goldeneas/potxii/src/led_pwm.py

from machine import Pin, PWM

class LedPWM:
    def __init__(self, pin_id, max_pwm_value=1023):
        self._pin = Pin(pin_id, Pin.OUT)
        self._max_pwm_value = max_pwm_value
        self._pwm = PWM(self._pin)
        self.set_brightness(0)

    def off(self):
        self.set_brightness(0)
        
    def on(self):
        self.set_brightness(100)

    # value between 0 and 100
    def set_brightness(self, value=50):
        self._pwm.duty(int(value / 100 * self._max_pwm_value))
