goldeneas/potxii/test/oled_test.py

#main
from machine import Pin, I2C
from time import sleep
import ssd1306

WIDTH = 128
HEIGHT = 64
SCL_PIN = 22
SDA_PIN = 21

i2c = I2C(0, scl=Pin(SCL_PIN), sda=Pin(SDA_PIN))
display = ssd1306.SSD1306_I2C(WIDTH, HEIGHT, i2c)

display.draw_logo()
sleep(3)

robin = bytearray(b'\x00\x01\xff\xff\xff\xff\xff\xff\xff\xff\xff\xff\xff\xff\xf0\x00\x00\x07\xff\xff\xff\xff\xff\xff\xff\xff\xff\xff\xff\xff\xfc\x00\x00\x0f\xff\xff\xff\xff\xff\xff\xff\xff\xff\xff\xff\xff\xfc\x00\x00\x1f\xff\xff\xff\xff\xff\xff\xff\xff\xff\xff\xff\xff\xfe\x00\x00\x1f\xff\xff\xff\xff\xff\xff\xff\xff\xff\xff\xff\xff\xfe\x00\x00\x1f\xff\xff\xff\xff\xff\xff\xff\xff\xff\xff\xff\xff\xfe\x00\x00\x1f\xff\xff\xff\xff\xff\xff\xff\xff\xff\xff\xff\xff\xfe\x00\x00\x1f\xff\xff\xf8\x1f\xff\xff\xff\xff\xf8\x1f\xff\xff\xfe\x00\x00\x3f\xff\xfd\xfe\x3f\xe7\xff\xff\xe7\xfc\x7f\xbf\xff\xff\x00\x00\x3f\xff\xf7\x03\xc0\x3d\xff\xff\xbc\x03\xc0\xef\xff\xff\x00\x00\x3f\xff\xdd\xff\xff\xf3\xff\xff\xff\xff\xff\xbb\xff\xff\x00\x00\x7f\xff\xf7\xff\xff\xfd\xdf\xfb\xbf\xff\xff\xcf\xff\xff\x80\x00\x7f\xff\x2f\xff\xff\xfe\xdc\x3b\x7f\xff\xff\xcc\xff\xff\xc0\x00\x7f\xfd\x2f\xff\xff\xfe\xec\x37\x7f\xff\xff\xcc\xbf\xff\xc0\x00\x7f\xfd\x2f\xff\xff\xff\x27\xe4\xff\xff\xff\xcc\xbf\xff\xc0\x00\x7f\xfd\x37\xff\xff\xfe\xef\xf7\x7f\xff\xff\xcc\xbf\xff\xc0\x00\x7f\xfd\x17\xff\xff\xfc\xdf\xfb\x7f\xff\xff\xc8\xbf\xff\xc0\x00\x7f\xfb\x2d\xff\xff\xfd\xbf\xfd\xbf\xff\xff\xb4\xdf\xff\xc0\x00\x7f\xfb\x2e\x3f\xff\xf3\xff\xff\xcf\xff\xfc\x77\xdf\xff\xc0\x00\x7f\xfa\xf7\xe3\xfe\x0e\xff\xff\x70\x7f\xc7\xef\x77\xff\xc0\x00\x3f\xfa\xff\xff\xcf\xff\xff\xff\xff\xf3\xff\xff\x77\xff\x00\x00\x3f\xee\xff\xf8\x78\xff\xff\xff\xff\x1e\x1f\xff\xb7\xff\x00\x00\x1f\xed\xff\xff\xff\xff\xff\xff\xff\xff\xff\xff\xbb\xfe\x00\x00\x1f\xed\xff\xff\xff\xff\xff\xff\xff\xff\xff\xff\xbb\xfe\x00\x00\x0f\xcd\xff\xff\xff\xff\xff\xff\xff\xff\xff\xff\xdb\xfe\x00\x00\x07\xdd\xff\xff\xff\xff\xff\xff\xff\xff\xff\xff\xdd\xfc\x00\x00\x07\xdb\xff\xff\xff\xf8\x00\x03\xff\xff\xff\xff\xf5\xfc\x00\x00\x07\xdb\xff\xff\xff\x00\x00\x3e\x3f\xff\xff\xff\xf5\xf8\x00\x00\x03\xdb\xff\xff\x80\x00\x00\xff\xfc\xff\xff\xff\xf5\xf8\x00\x00\x03\xdb\xff\xf0\x00\x00\x07\xff\xff\x8f\xff\xff\xf6\x70\x00\x00\x01\xdb\xff\xc0\x00\x00\x1f\xff\xff\xfb\xff\xff\xf6\x60\x00\x00\x01\xaf\xff\x00\x00\x01\xff\xff\xff\xfe\xff\xff\xfa\x60\x00\x00\x00\x2f\xfc\x00\x00\x0f\xff\xff\xff\xfb\x3f\xff\xfb\xa0\x00\x00\x00\x27\xf8\x00\x0c\xf0\xff\xfc\x3f\xde\x0f\xff\xf5\x80\x00\x00\x00\x2f\xf0\x03\x00\x07\xbf\xf3\x86\x32\x03\xff\xf1\x80\x00\x00\x00\x19\xe0\x00\x00\x00\xef\xef\x60\x05\x00\xff\xfa\x00\x00\x00\x00\x0f\xc0\x00\x0f\x21\xf7\xf9\x8f\x00\x00\x3f\xfc\x00\x00\x00\x00\x1f\x80\x03\xce\x2f\xff\xff\xce\x2f\x00\x6f\xfe\x00\x00\x00\x00\x3e\xe0\x07\xc8\x6d\xff\xff\xc8\x6f\xc0\x3b\xff\xc0\x00\x00\x00\xfe\x40\x07\x27\xd3\xff\xff\xa7\xd1\xc0\x68\xff\xe0\x00\x00\x03\xfc\xe0\x07\xe0\x3f\xf9\x3f\xf0\x1f\xc0\x78\x1f\xfc\x00\x00\x0f\xf0\x80\x07\xff\xff\xf9\x7f\xff\xff\xc0\x10\x37\xff\x00\x00\x07\xd0\x80\x0f\xff\xff\xf9\x7f\xff\xff\xe0\x10\x3f\xfe\x00\x00\x03\xf0\x80\x0f\xff\xff\xf9\x7f\xff\xff\xe0\x00\x0f\xf8\x00\x00\x00\xfc\x00\x0f\xff\xff\xf9\x7f\xff\xff\xe0\x00\x07\xf0\x00\x00\x00\x1c\x00\x0f\xff\xff\xf9\x7f\xff\xff\xe0\x00\x07\x80\x00\x00\x00\x00\x00\x1f\xff\xff\xfe\xff\xff\xff\xf0\x00\x00\x00\x00\x00\x00\x00\x00\x0f\xff\xff\xff\xff\xff\xff\xe0\x00\x00\x00\x00\x00\x00\x00\x00\x0f\xff\xff\xff\xff\xff\xff\xe0\x00\x00\x00\x00\x00\x00\x00\x00\x17\xff\xff\xff\xff\xff\xff\xc0\x00\x00\x00\x00\x00\x00\x02\x00\x07\xff\xff\xff\xff\xff\xff\x98\x00\x00\x00\x00\x00\x00\x03\x00\x03\xff\xff\xcf\xf3\xff\xff\x00\x00\x04\x00\x00\x00\x00\x01\x00\x00\xff\xff\xff\xff\xff\xfe\x00\x00\x00\x40\x00\x00\x00\x00\x00\x00\x7f\xff\xff\xff\xff\xfc\x00\x00\x02\x00\x00\x00\x00\x00\x00\x00\x1f\xff\xf8\x1f\xff\xf0\x00\x00\x00\x20\x00\x00\x00\x00\x00\x00\x03\xff\xff\xff\xff\x00\x00\x00\x00\x00\x00\x00\x00\x00\x00\x00\x02\xff\xff\xff\xfd\x00\x00\x00\x00\x00\x00\x00\x00\x00\x00\x00\x01\x87\xff\xff\xe3\x00\x00\x00\x00\x00\x00\x00\x00\x00\x00\x00\x01\xfc\xff\xfc\x7e\x00\x00\x00\x00\x00\x00\x00\x00\x00\x00\x00\x00\xff\x8f\xe3\xfc\x00\x00\x00\x00\x00\x00\x00\x00\x00\x00\x00\x00\x7f\xf7\x9f\xfc\x00\x00\x00\x00\x00\x00\x00\x00\x00\x00\x00\x00\x7f\xfc\x7f\xfc\x00\x00\x00\x00\x00\x00\x00\x00\x00\x00\x00\x00\x7f\xff\xff\xfc\x00\x00\x00\x00\x00\x00\x00\x00\x00\x00\x00\x01\xff\xff\xff\xfe\x00\x00\x00\x00\x00\x00')
display.draw_image(robin, 128, 64, 0, 0)
sleep(3)
